tenorangesax/The-SaxplayerTM/PICTURES/FINAL/back silk.png

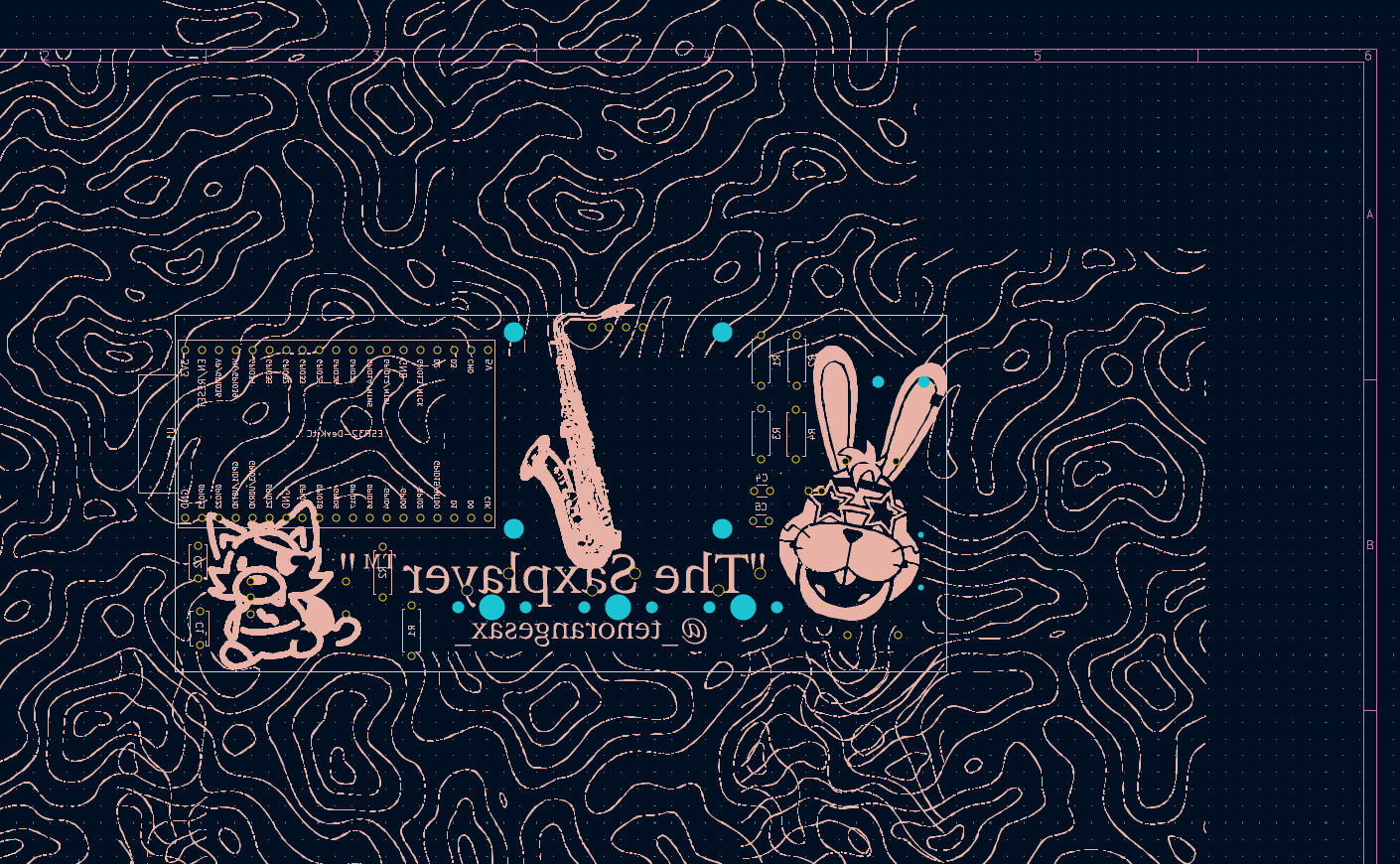
PICTURES/FINAL/back silk.png
