tenorangesax/The-SaxplayerTM/PICTURES/FINAL/Back_final.png

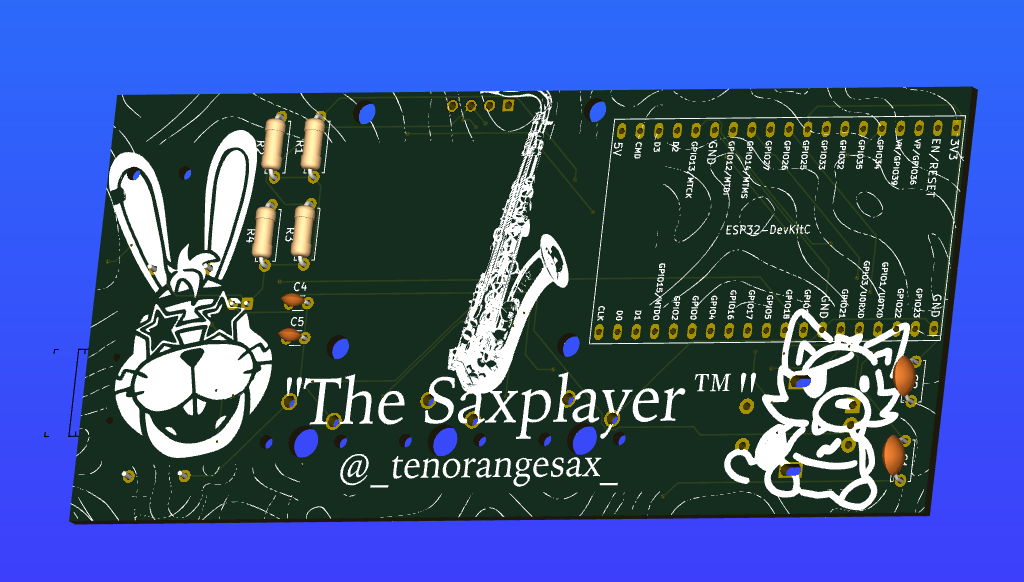
PICTURES/FINAL/Back_final.png
