tenorangesax/The-SaxplayerTM/PICTURES/FINAL/footprints.png

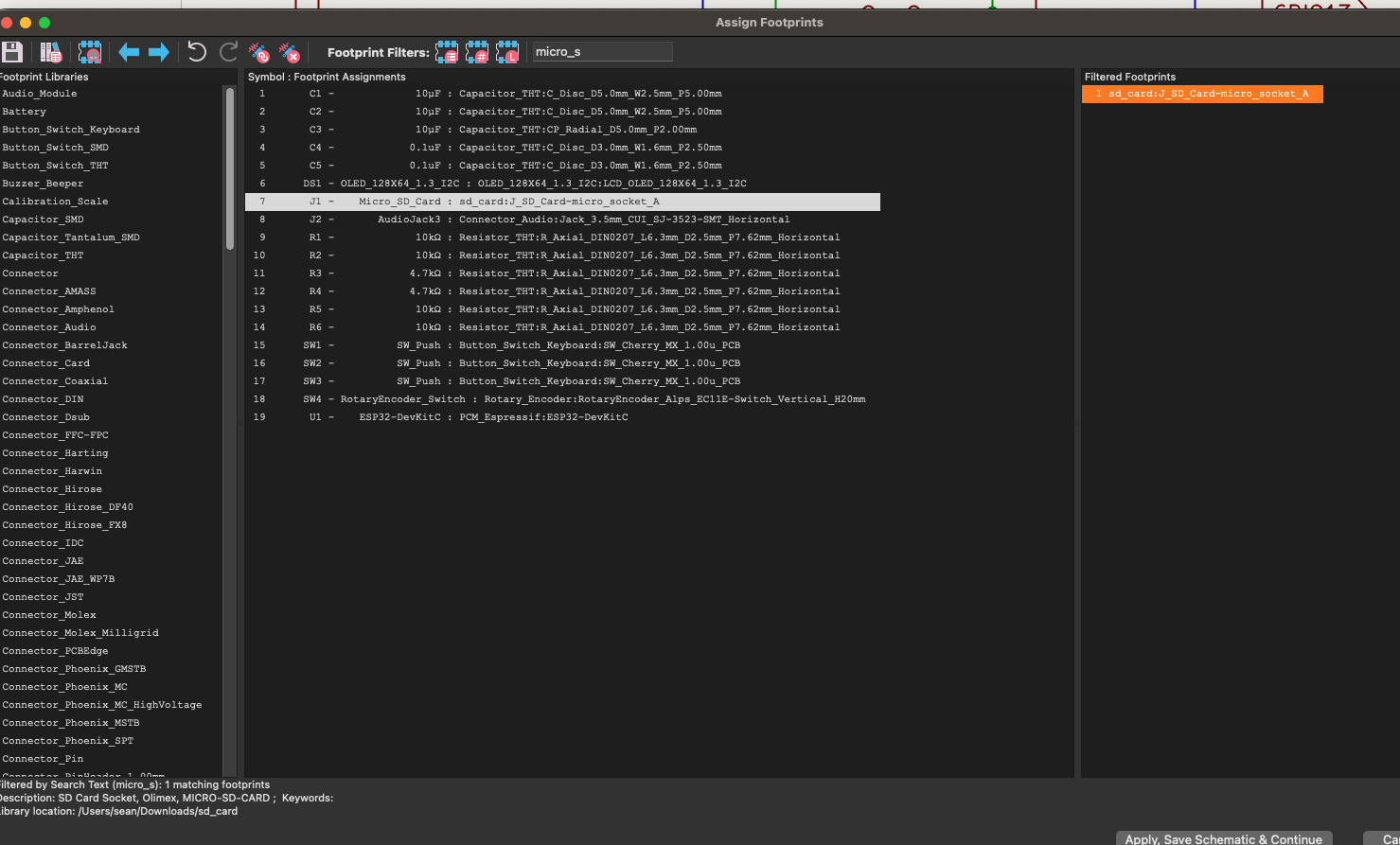
PICTURES/FINAL/footprints.png
