tenorangesax/The-SaxplayerTM/PICTURES/FINAL/front silk.png

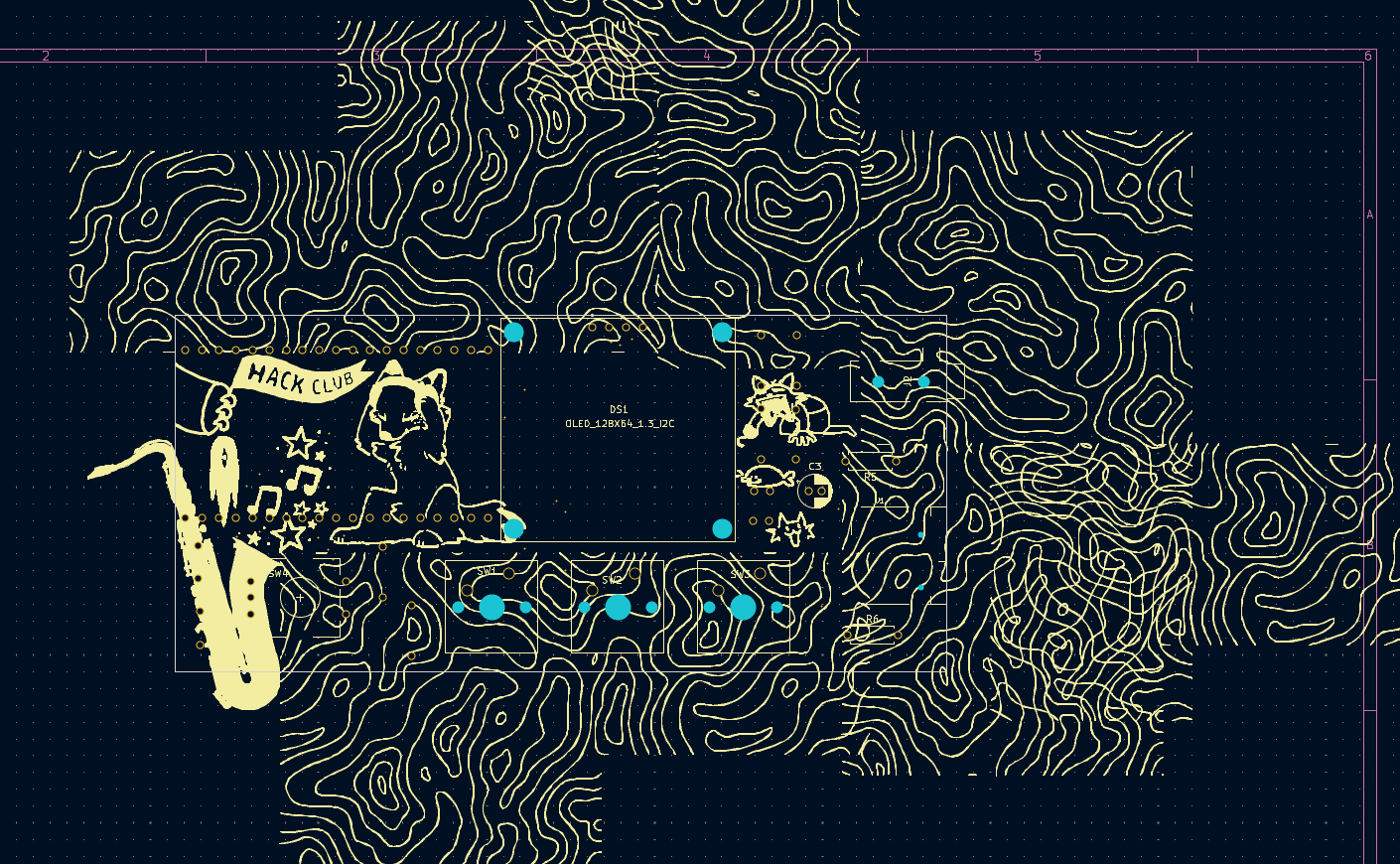
PICTURES/FINAL/front silk.png
