tenorangesax/The-SaxplayerTM/PICTURES/FINAL/IMG_7595.jpeg

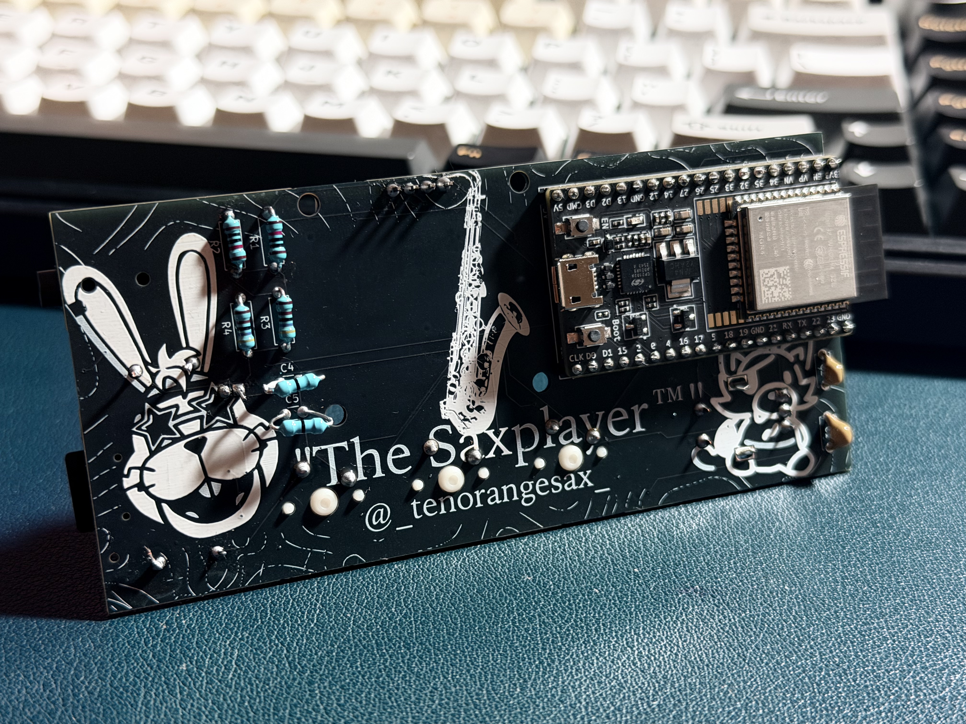
PICTURES/FINAL/IMG_7595.jpeg
