tenorangesax/The-SaxplayerTM/PICTURES/FINAL/IMG_7597.jpeg

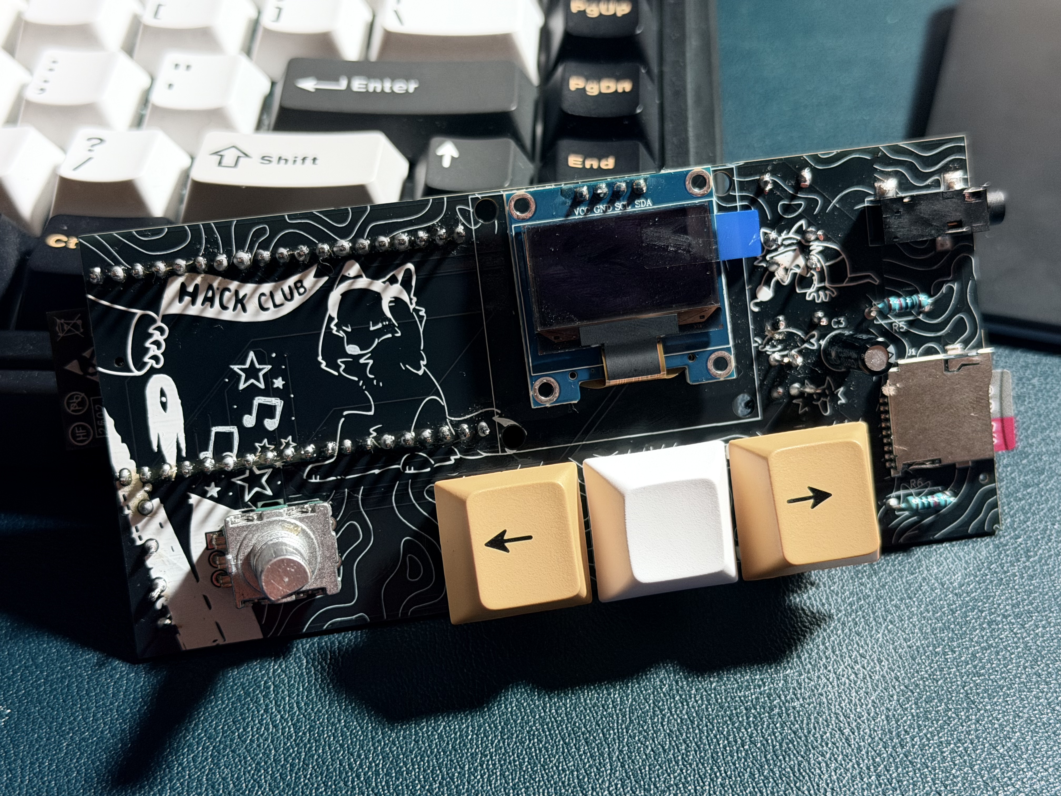
PICTURES/FINAL/IMG_7597.jpeg
