tenorangesax/The-SaxplayerTM/PICTURES/FINAL/IMG_7604.jpeg

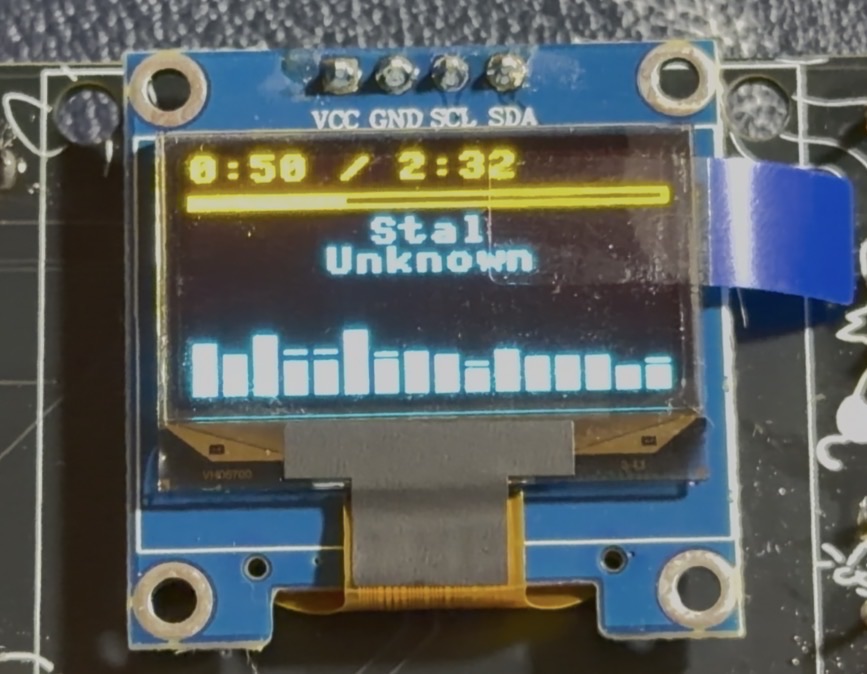
PICTURES/FINAL/IMG_7604.jpeg
