tenorangesax/The-SaxplayerTM/PICTURES/FINAL/IMG_7605.jpeg

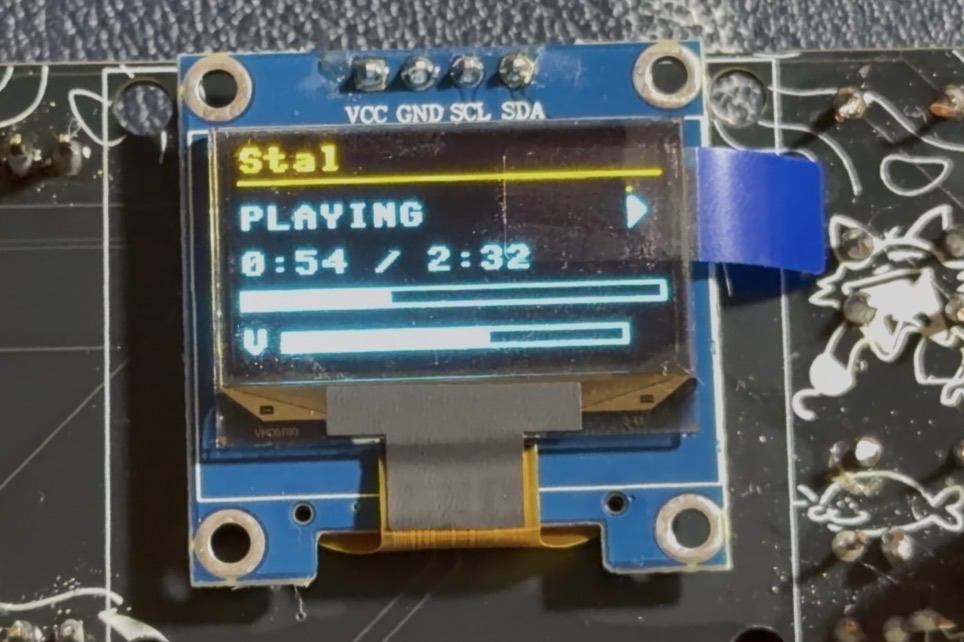
PICTURES/FINAL/IMG_7605.jpeg
