tenorangesax/The-SaxplayerTM/PICTURES/FINAL/IMG_7606.jpeg

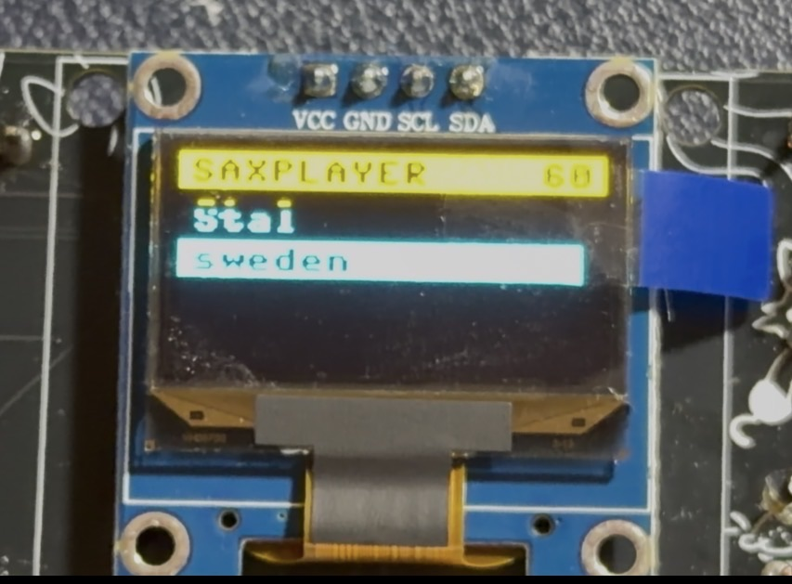
PICTURES/FINAL/IMG_7606.jpeg
