tenorangesax/The-SaxplayerTM/PICTURES/FINAL/IMG_7608.jpeg

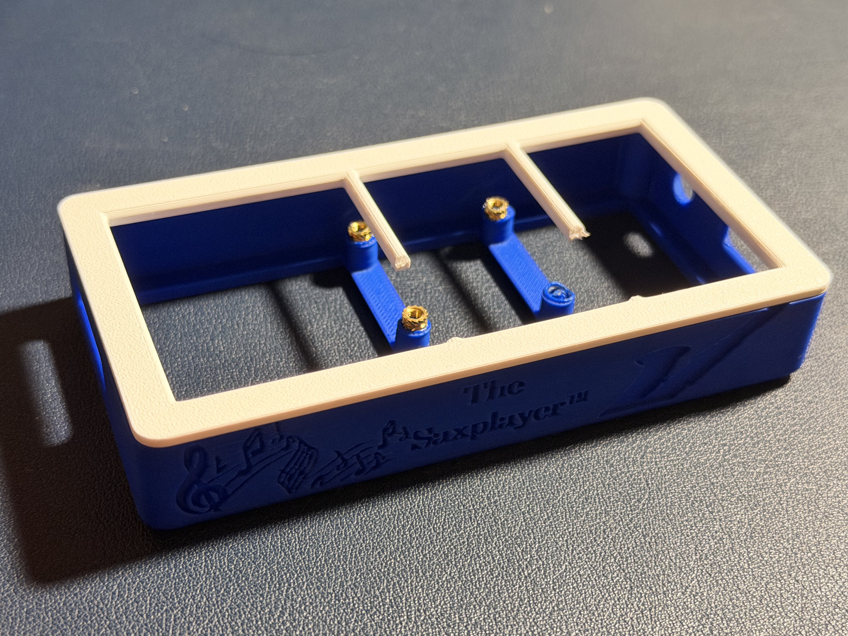
PICTURES/FINAL/IMG_7608.jpeg
