tenorangesax/The-SaxplayerTM/PICTURES/FINAL/IMG_7609.jpeg

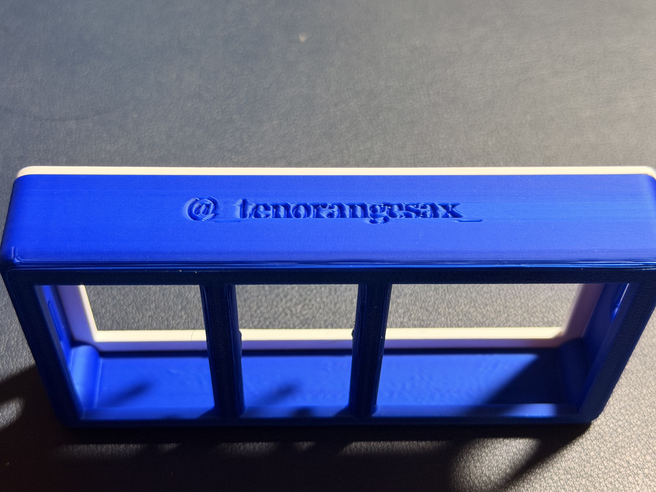
PICTURES/FINAL/IMG_7609.jpeg
