tenorangesax/The-SaxplayerTM/PICTURES/FINAL/IMG_7610.jpeg

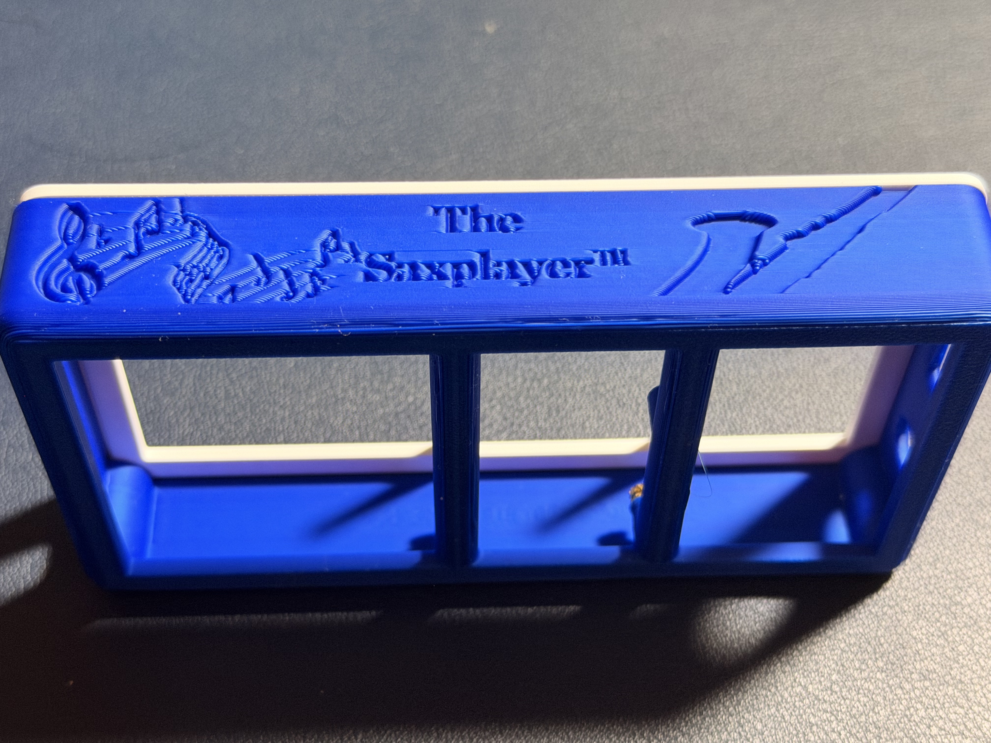
PICTURES/FINAL/IMG_7610.jpeg
