tenorangesax/The-SaxplayerTM/PICTURES/FINAL/IMG_7611.jpeg

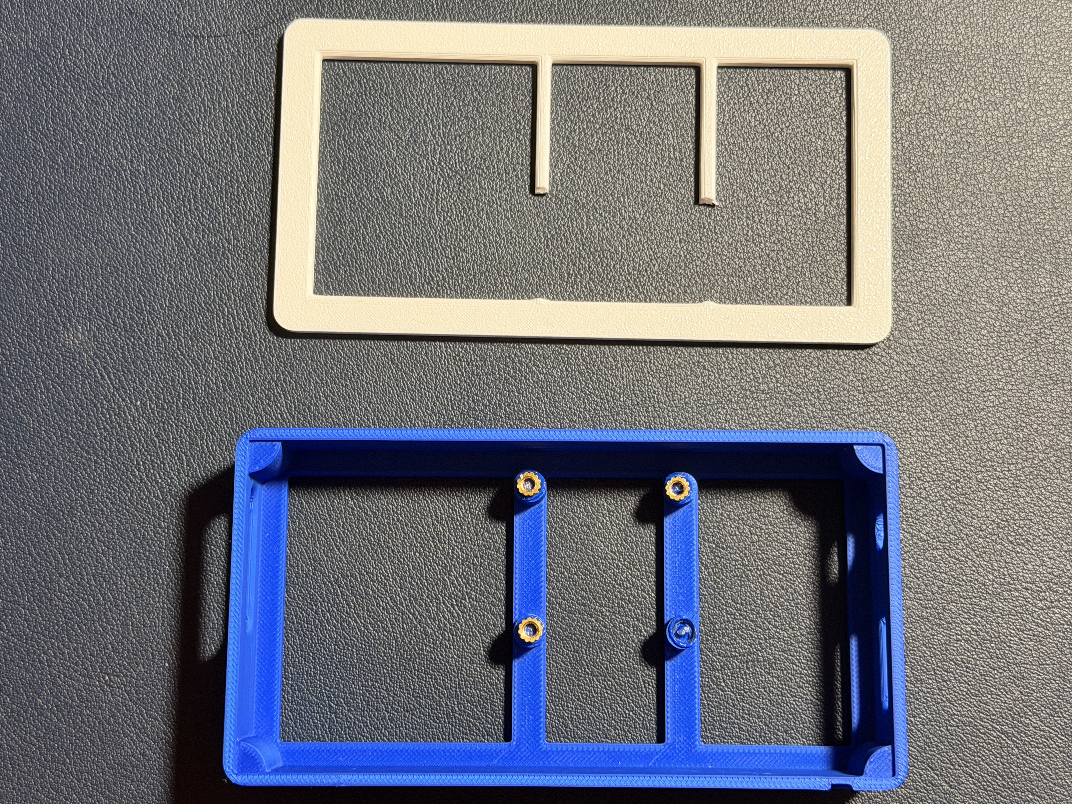
PICTURES/FINAL/IMG_7611.jpeg
