tenorangesax/The-SaxplayerTM/PICTURES/FINAL/IMG_7619.jpeg

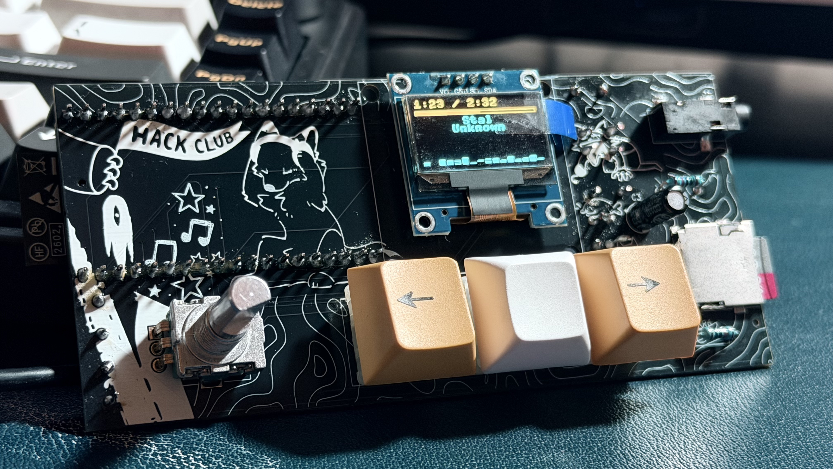
PICTURES/FINAL/IMG_7619.jpeg
