tenorangesax/The-SaxplayerTM/PICTURES/FINAL/JLCPCB BACK.png

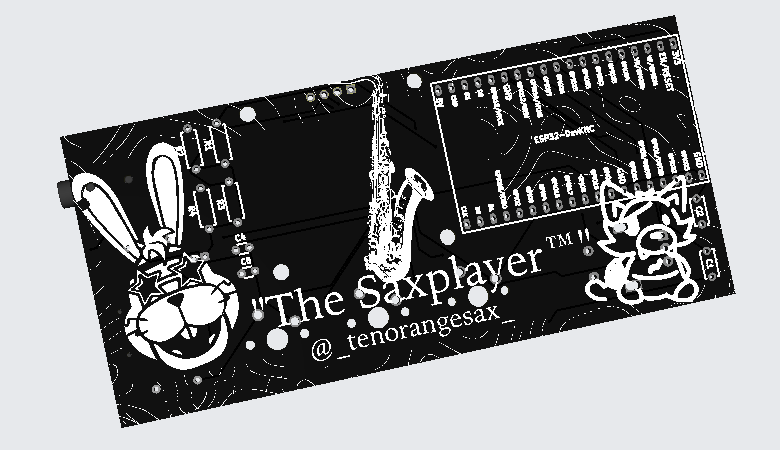
PICTURES/FINAL/JLCPCB BACK.png
