tenorangesax/The-SaxplayerTM/PICTURES/FINAL/JLCPCB FRONT.png

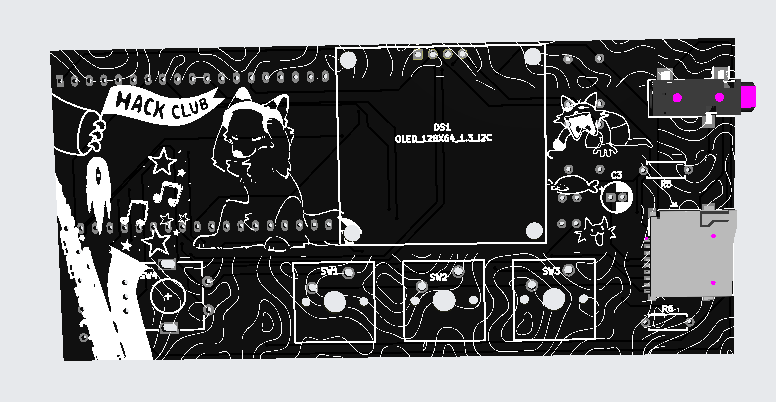
PICTURES/FINAL/JLCPCB FRONT.png
