tenorangesax/The-SaxplayerTM/PICTURES/FINAL/more footprints.png

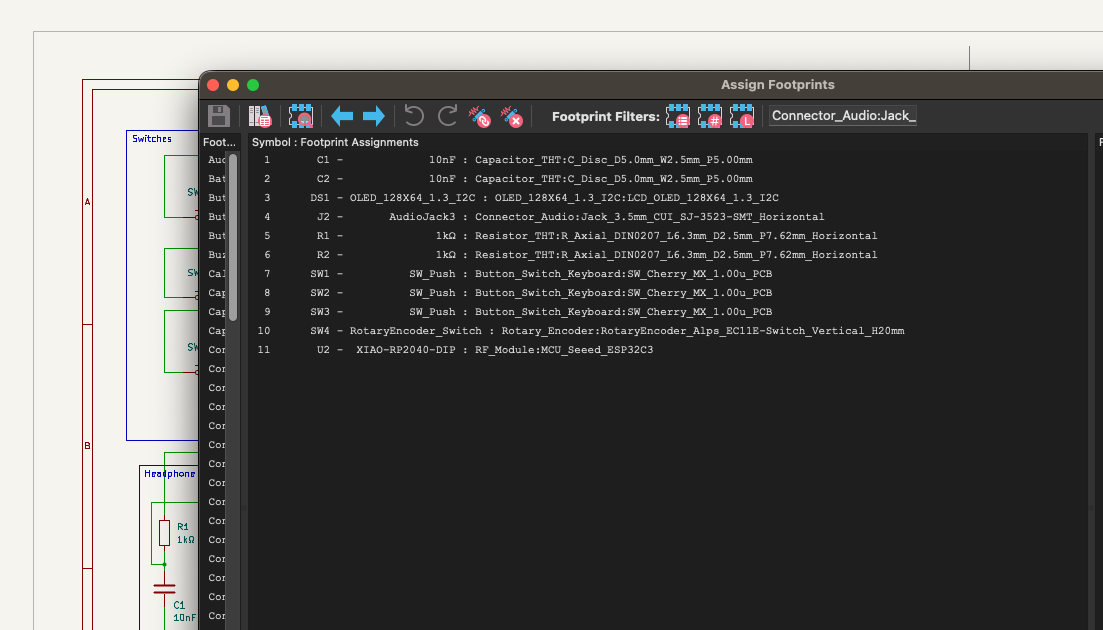
PICTURES/FINAL/more footprints.png
