tenorangesax/The-SaxplayerTM/PICTURES/FINAL/negative warnings???.png

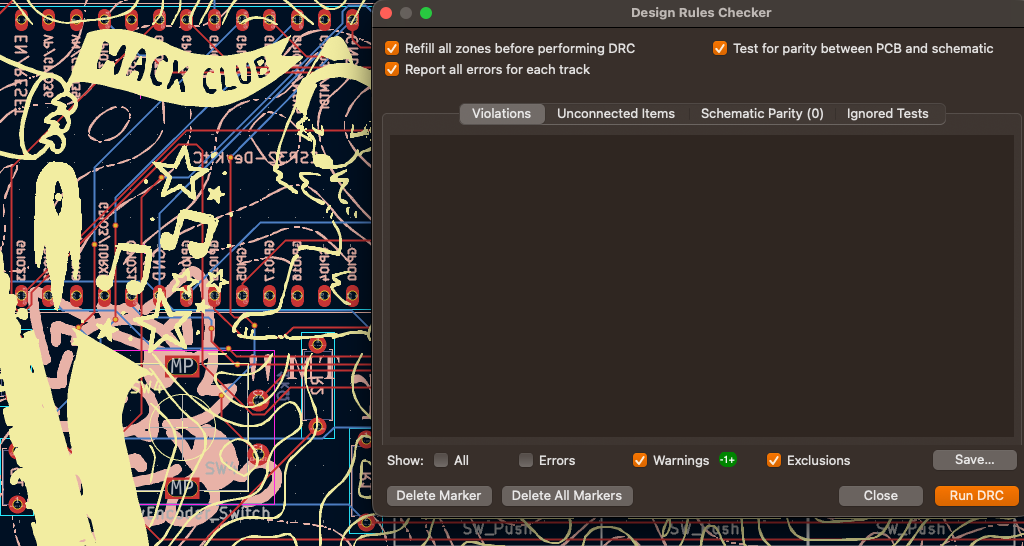
PICTURES/FINAL/negative warnings???.png
