tenorangesax/The-SaxplayerTM/PICTURES/FINAL/Saxplayer_Case_Alt_View.png

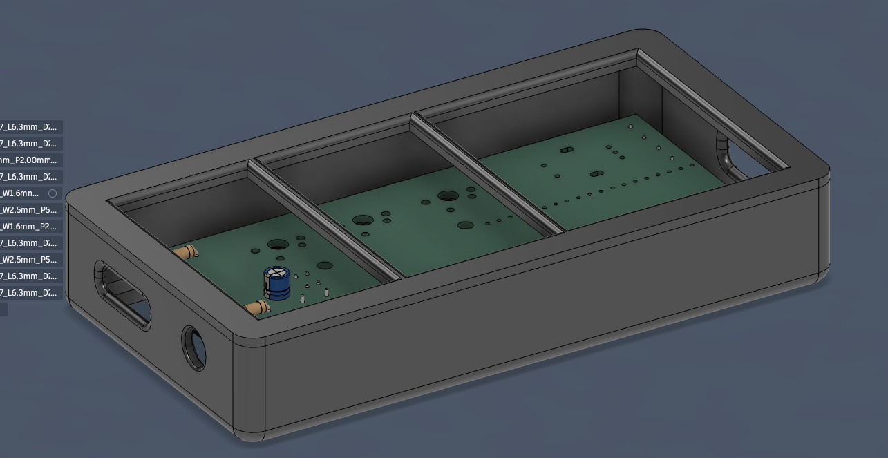
PICTURES/FINAL/Saxplayer_Case_Alt_View.png
