tenorangesax/The-SaxplayerTM/PICTURES/FINAL/Saxplayer_Case_Bottom.png

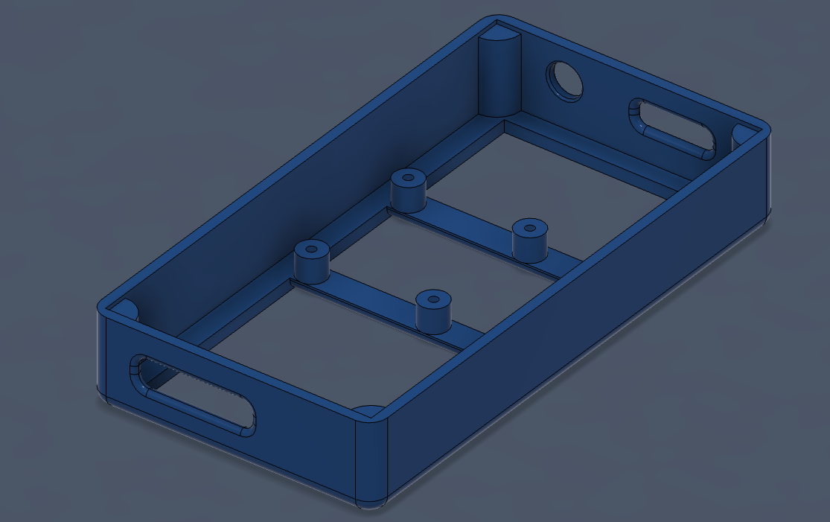
PICTURES/FINAL/Saxplayer_Case_Bottom.png
