tenorangesax/The-SaxplayerTM/PICTURES/FINAL/Saxplayer_Case_Full.png

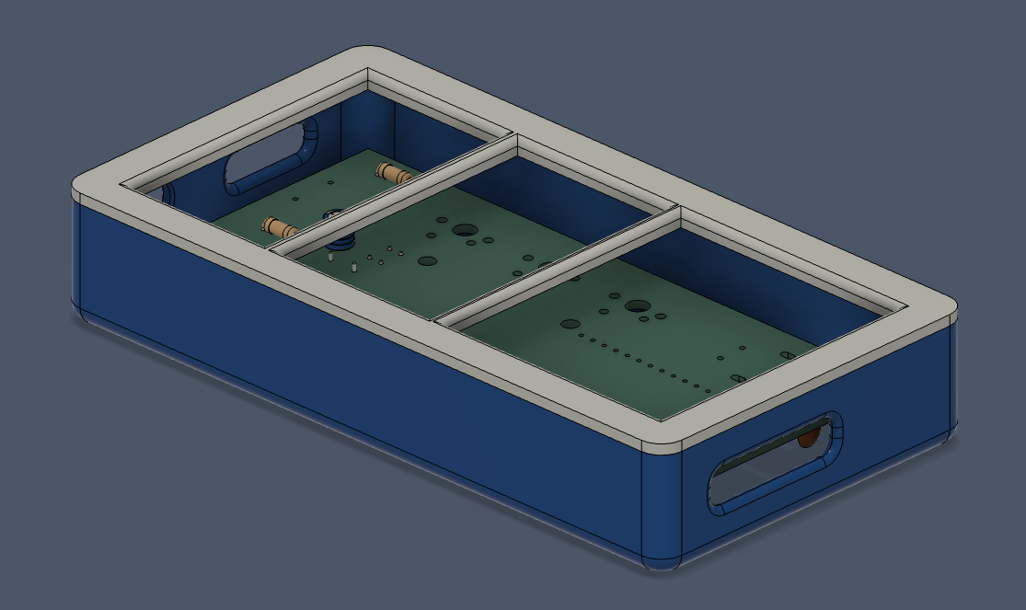
PICTURES/FINAL/Saxplayer_Case_Full.png
