tenorangesax/The-SaxplayerTM/PICTURES/FINAL/Saxplayer_Case_Top.png

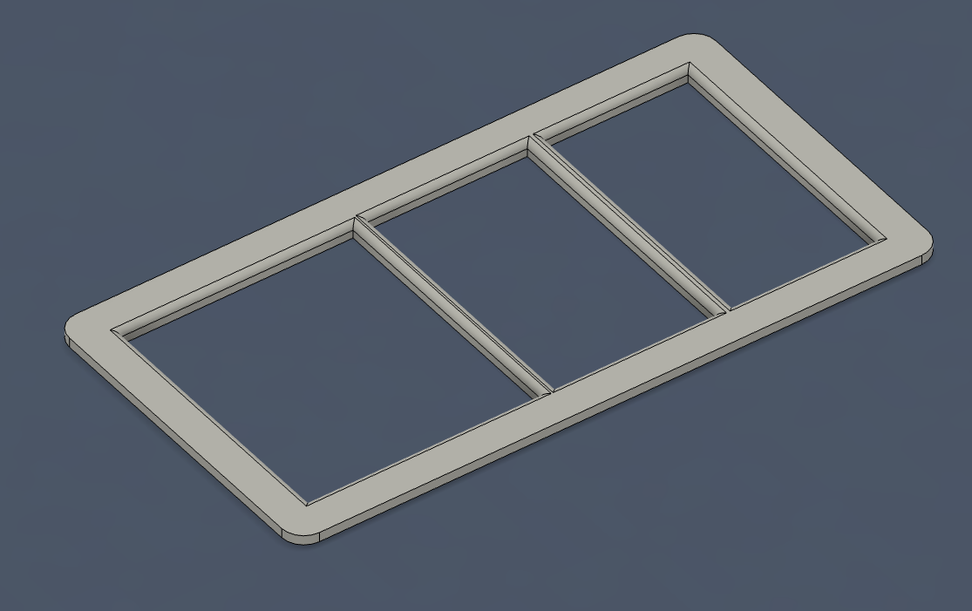
PICTURES/FINAL/Saxplayer_Case_Top.png
