tenorangesax/The-SaxplayerTM/PICTURES/FINAL/the whole mess.png

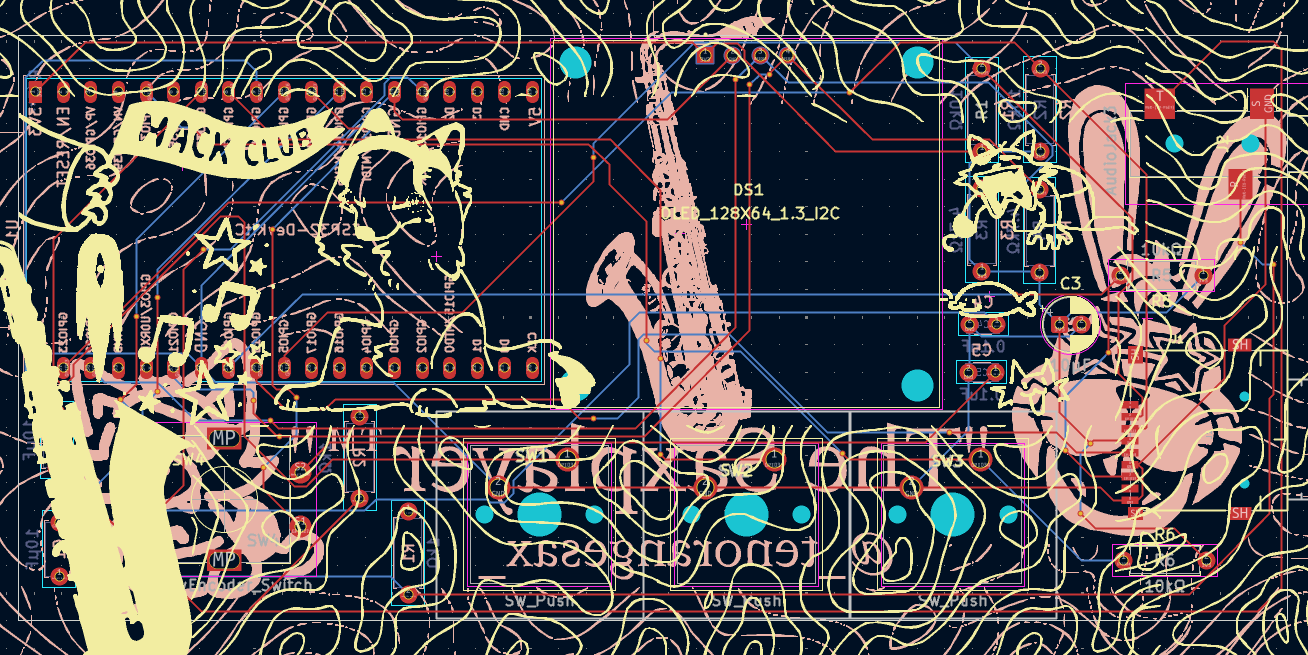
PICTURES/FINAL/the whole mess.png
