tenorangesax/The-SaxplayerTM/Extra_Materials/_ (1).jpeg

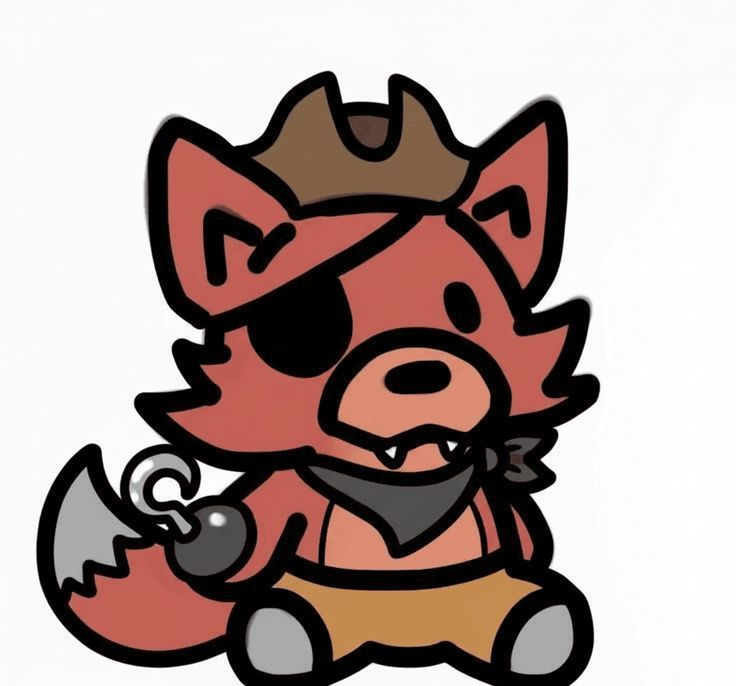
Extra_Materials/_ (1).jpeg
