tenorangesax/The-SaxplayerTM/Extra_Materials/_ (2).jpeg

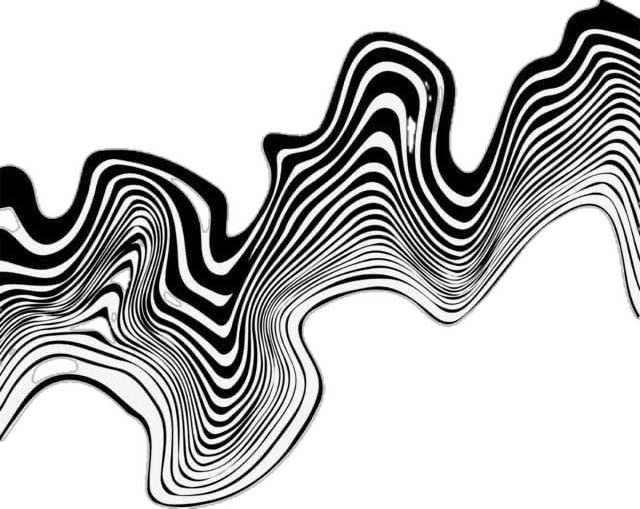
Extra_Materials/_ (2).jpeg
