tenorangesax/The-SaxplayerTM/Extra_Materials/_ (3).jpeg

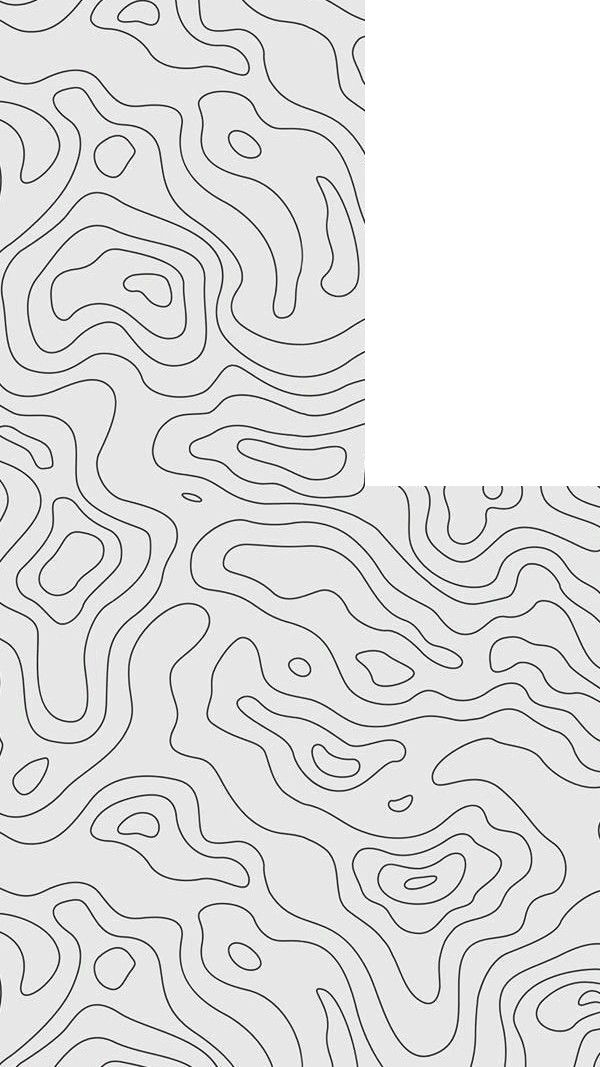
Extra_Materials/_ (3).jpeg
