tenorangesax/The-SaxplayerTM/Extra_Materials/_ (4).jpeg

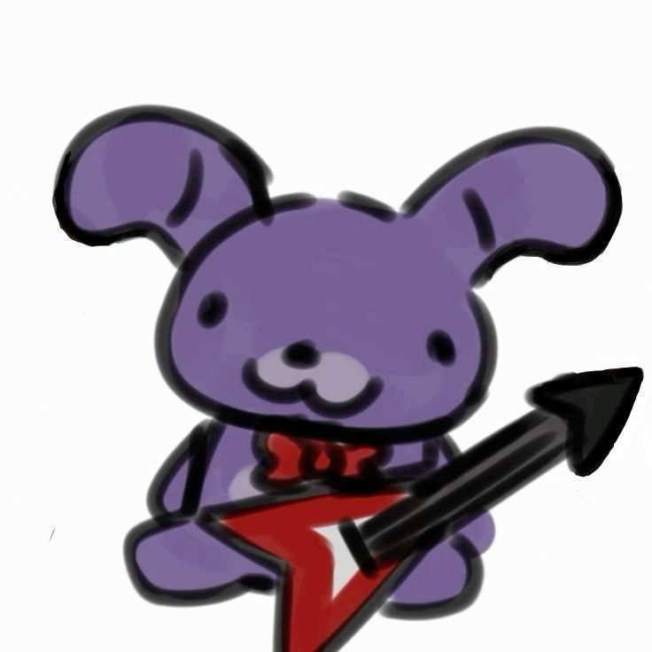
Extra_Materials/_ (4).jpeg
