tenorangesax/The-SaxplayerTM/Extra_Materials/_ (5).jpeg

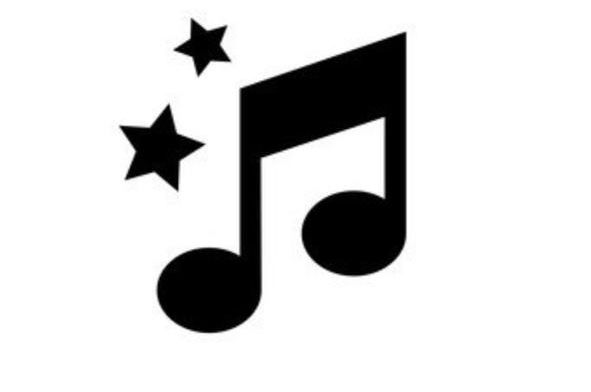
Extra_Materials/_ (5).jpeg
