tenorangesax/The-SaxplayerTM/Extra_Materials/_ (6).jpeg

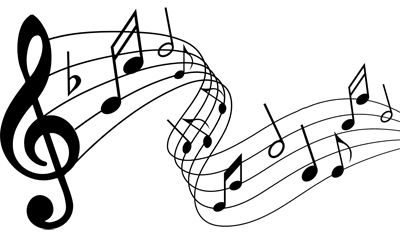
Extra_Materials/_ (6).jpeg
