tenorangesax/The-SaxplayerTM/Extra_Materials/_ (7).jpeg

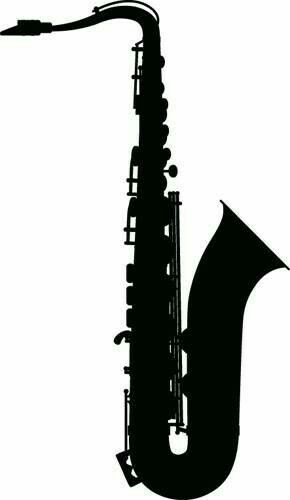
Extra_Materials/_ (7).jpeg
