tenorangesax/The-SaxplayerTM/Extra_Materials/_ (9).jpeg

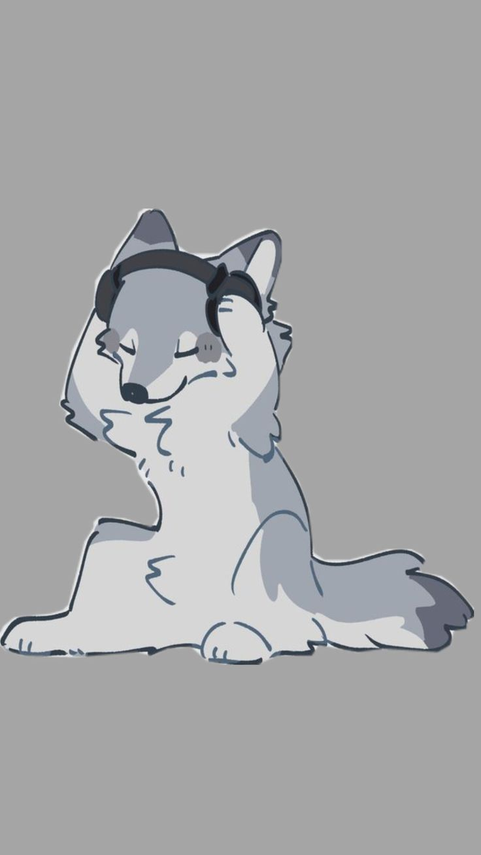
Extra_Materials/_ (9).jpeg
