tenorangesax/The-SaxplayerTM/Extra_Materials/_ (10).jpeg

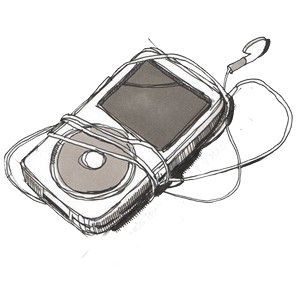
Extra_Materials/_ (10).jpeg
