tenorangesax/The-SaxplayerTM/Extra_Materials/_ (11).jpeg

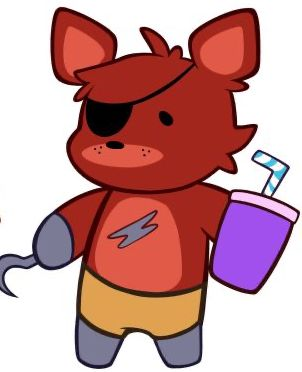
Extra_Materials/_ (11).jpeg
