tenorangesax/The-SaxplayerTM/Extra_Materials/_.jpeg

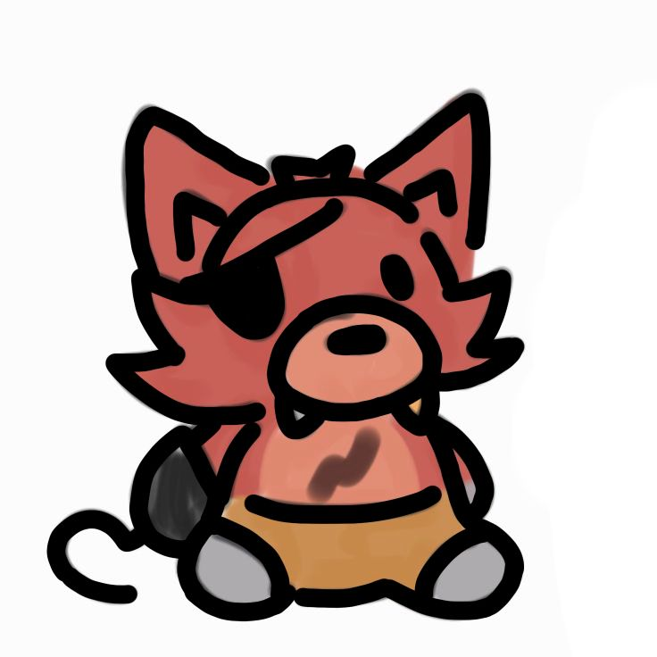
Extra_Materials/_.jpeg
