tenorangesax/The-SaxplayerTM/Extra_Materials/Download Saxophone, Sax, Woodwind_ Royalty-Free Vector Graphic.jpeg

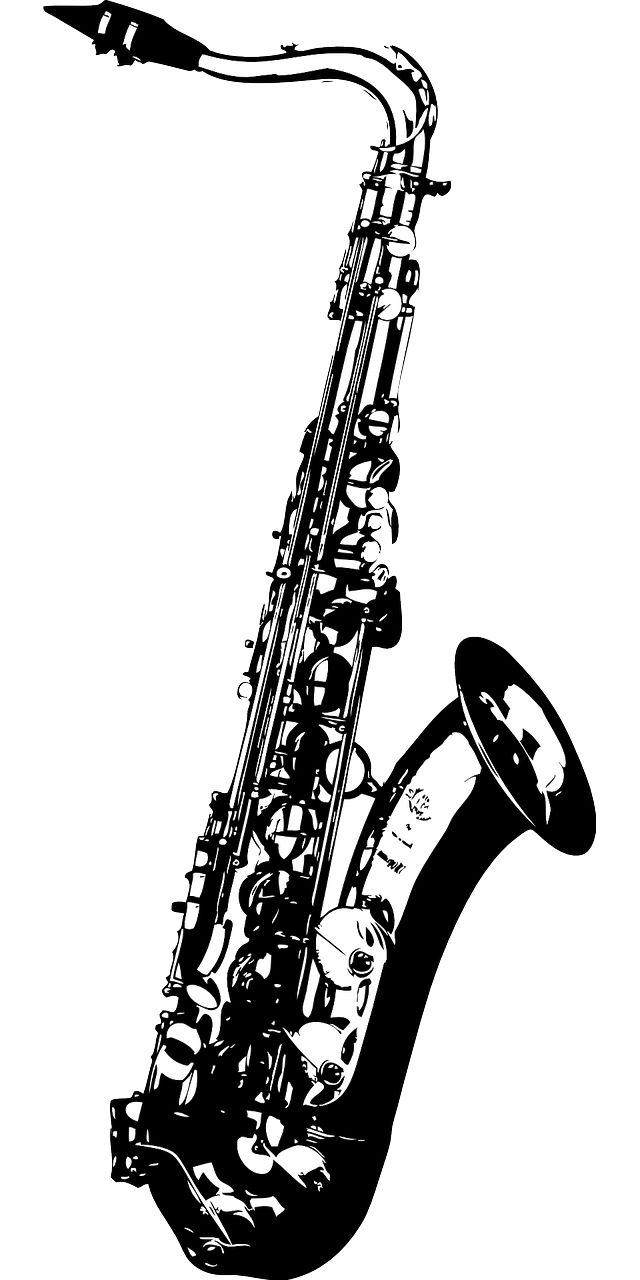
Extra_Materials/Download Saxophone, Sax, Woodwind_ Royalty-Free Vector Graphic.jpeg
