tenorangesax/The-SaxplayerTM/Extra_Materials/Follow me to get the best.jpeg

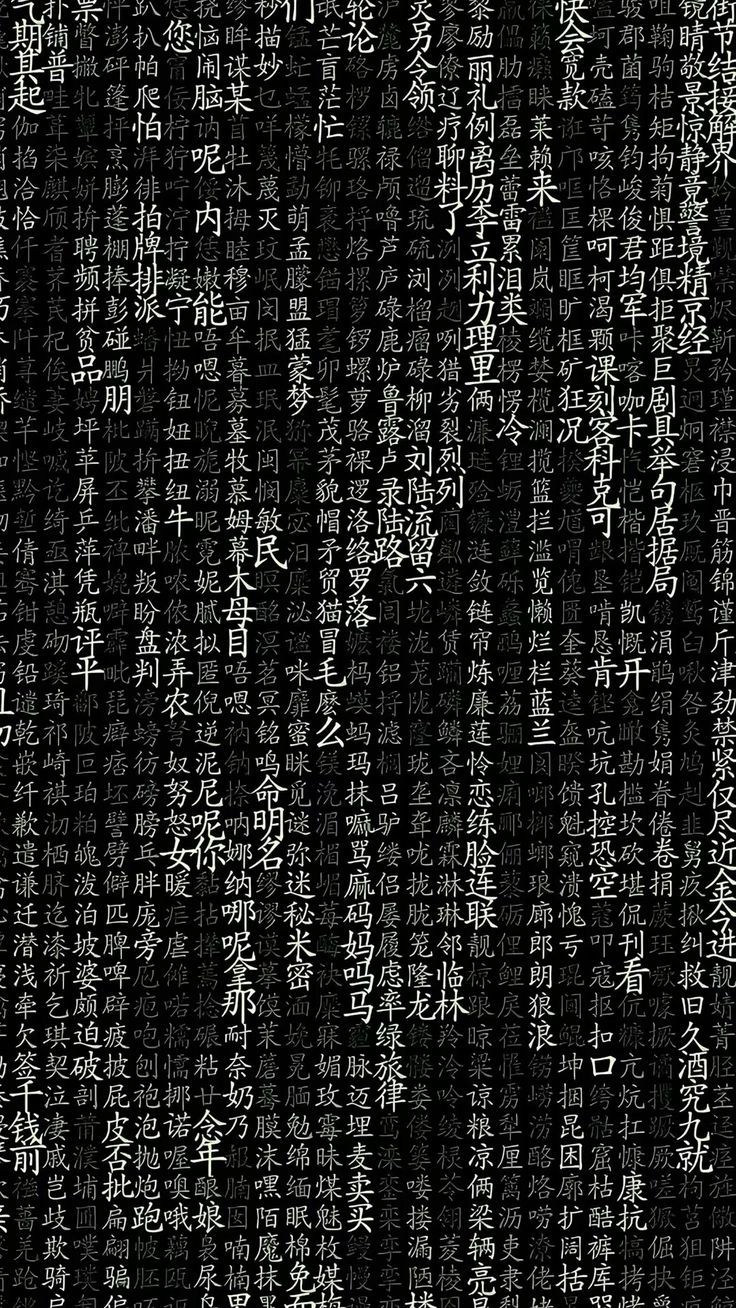
Extra_Materials/Follow me to get the best.jpeg
