tenorangesax/The-SaxplayerTM/Extra_Materials/Glamrock Bonnie Plush.jpeg

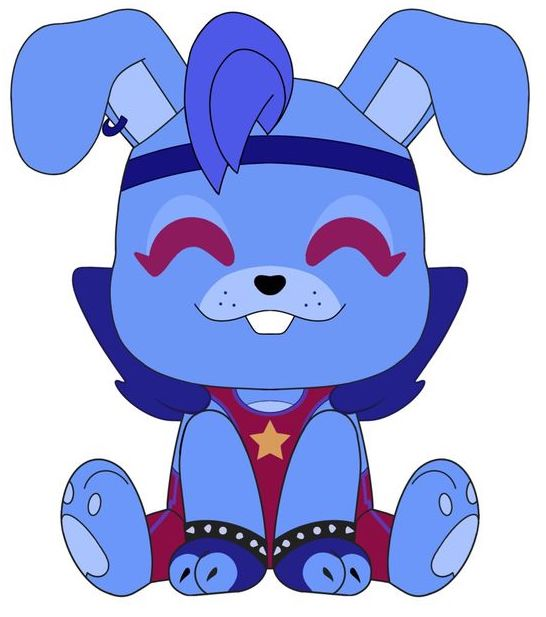
Extra_Materials/Glamrock Bonnie Plush.jpeg
