tenorangesax/The-SaxplayerTM/Extra_Materials/Silly cat _].jpeg

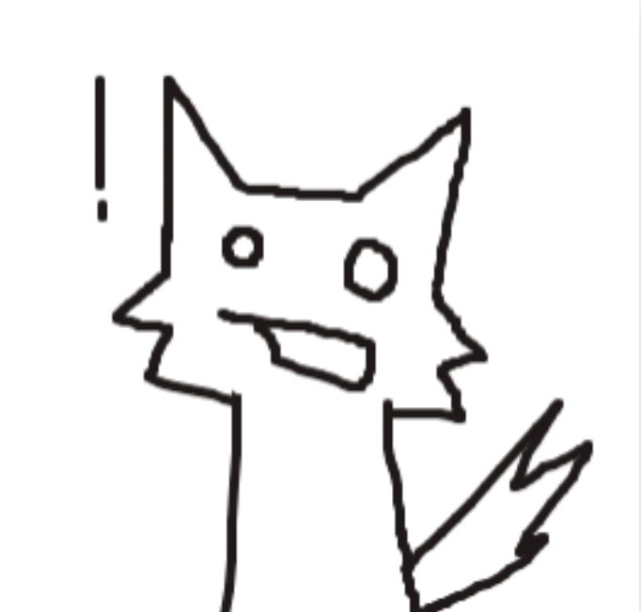
Extra_Materials/Silly cat _].jpeg
