tenorangesax/The-SaxplayerTM/Extra_Materials/theme!!.jpeg

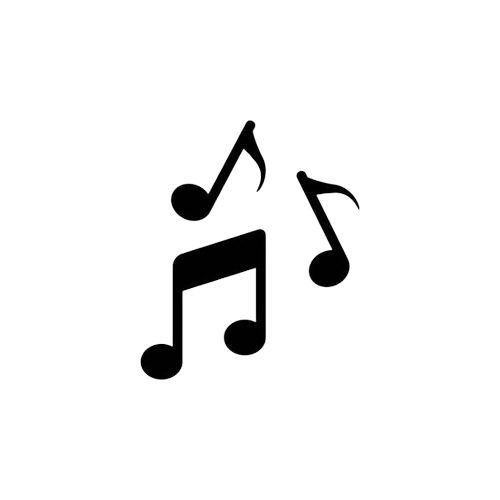
Extra_Materials/theme!!.jpeg
