tenorangesax/The-SaxplayerTM/PCB/Saxplayer.kicad_sch

## KiCad design PCB/Saxplayer.kicad_sch (2026-03-30)

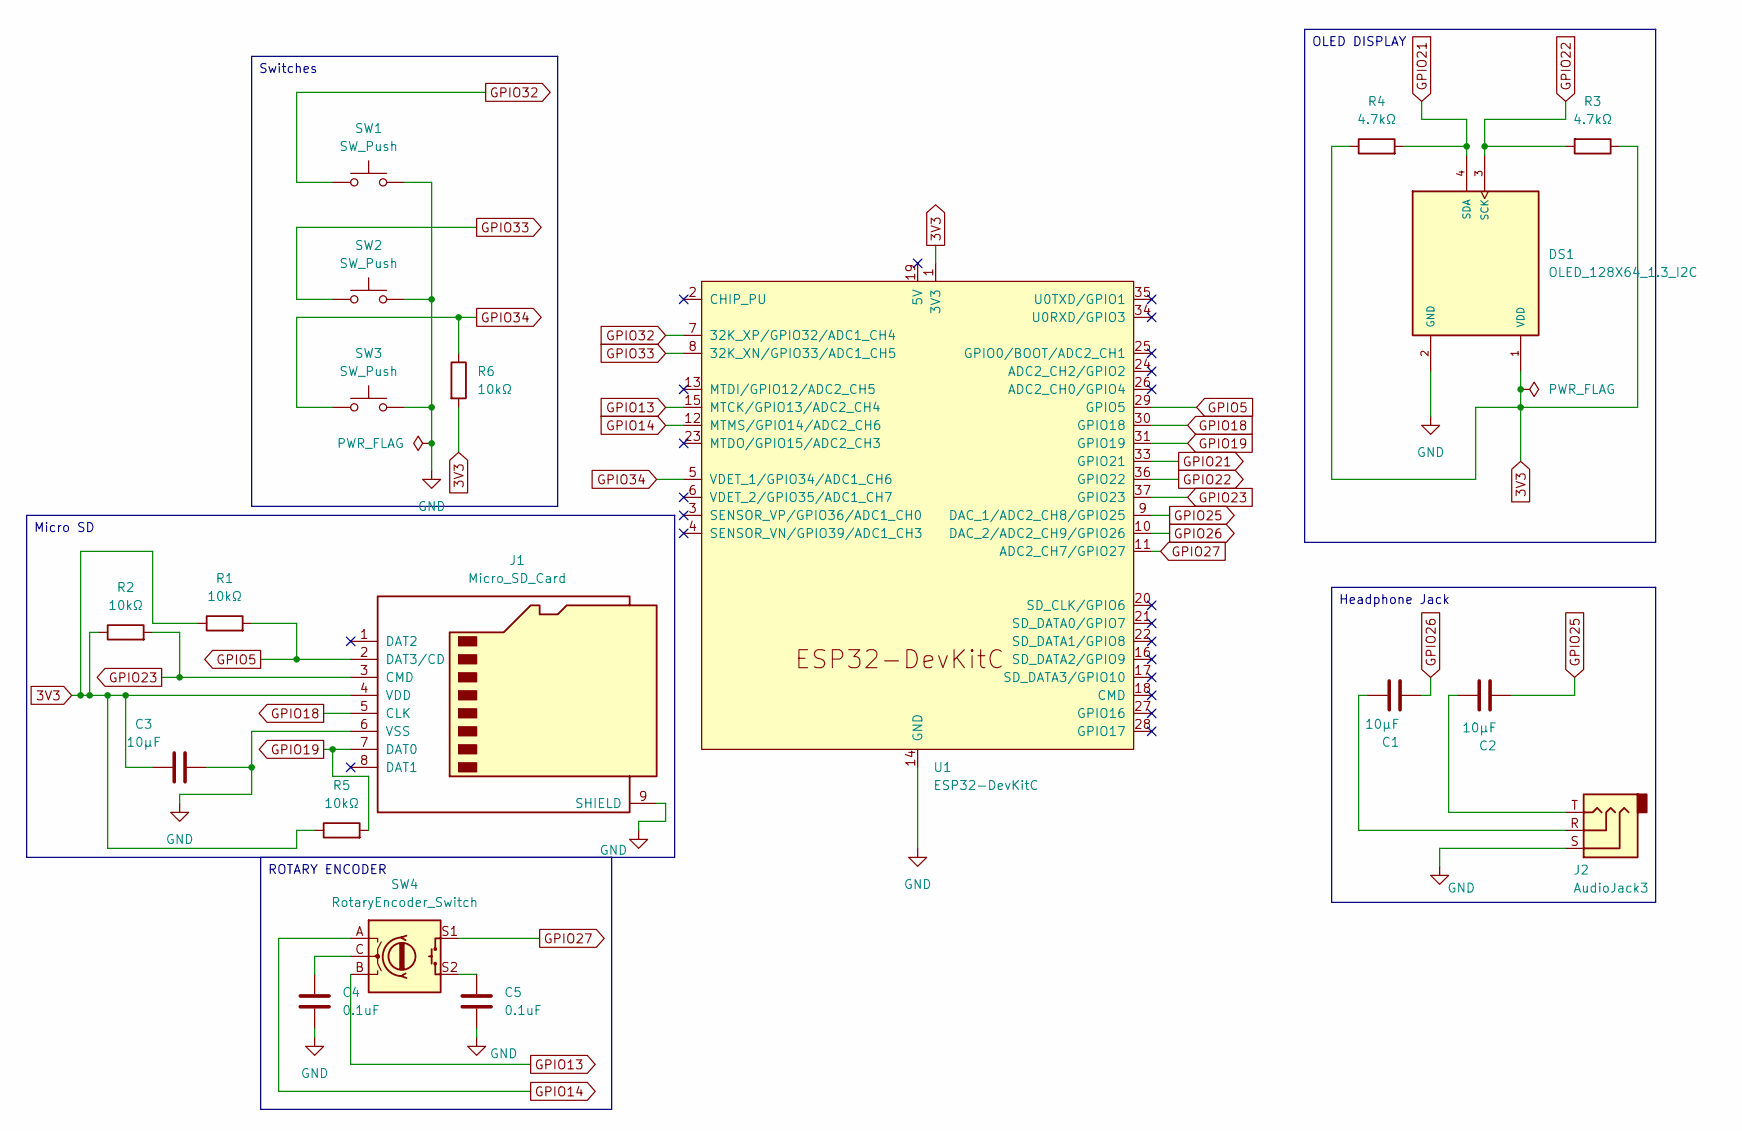
[picture p48: schematic Saxplayer.kicad_sch]

Parts:
C1, C2: 10µF; C_Disc_D5.0mm_W2.5mm_P5.00mm
C3: 10µF; CP_Radial_D5.0mm_P2.00mm
C4, C5: 0.1uF; C_Disc_D3.0mm_W1.6mm_P2.50mm
DS1: OLED_128X64_1.3_I2C; LCD_OLED_128X64_1.3_I2C; PARTREV NA
J1: Micro_SD_Card; J_SD_Card-micro_socket_A
J2: AudioJack3; Jack_3.5mm_CUI_SJ-3523-SMT_Horizontal
R1, R2, R5, R6: 10kΩ; R_Axial_DIN0207_L6.3mm_D2.5mm_P7.62mm_Horizontal
R3, R4: 4.7kΩ; R_Axial_DIN0207_L6.3mm_D2.5mm_P7.62mm_Horizontal
SW1, SW2, SW3: SW_Push; SW_Cherry_MX_1.00u_PCB
SW4: RotaryEncoder_Switch; RotaryEncoder_Alps_EC11E-Switch_Vertical_H20mm
U1: ESP32-DevKitC

Connections:
3V3: C3.1, DS1.1 (VDD), J1.4 (VDD), R1.1, R2.1, R3.1, R4.1, R5.1, R6.2, U1.1 (3V3)
GND: C3.2, C4.2, C5.2, DS1.2 (GND), J1.6 (VSS), J1.9 (SHIELD), J2.S, SW1.2, SW2.2, SW3.2, U1.14 (GND), U1.32 (GND), U1.38 (GND)
GPIO5: J1.2 (DAT3/CD), R1.2, U1.29 (GPIO5)
GPIO13: SW4.B, U1.15 (MTCK/GPIO13/ADC2_CH4)
GPIO14: SW4.A, U1.12 (MTMS/GPIO14/ADC2_CH6)
GPIO18: J1.5 (CLK), U1.30 (GPIO18)
GPIO19: J1.7 (DAT0), R5.2, U1.31 (GPIO19)
GPIO21: DS1.4 (SDA), R4.2, U1.33 (GPIO21)
GPIO22: DS1.3 (SCK), R3.2, U1.36 (GPIO22)
GPIO23: J1.3 (CMD), R2.2, U1.37 (GPIO23)
GPIO25: C2.2, U1.9 (DAC_1/ADC2_CH8/GPIO25)
GPIO26: C1.2, U1.10 (DAC_2/ADC2_CH9/GPIO26)
GPIO27: SW4.S1, U1.11 (ADC2_CH7/GPIO27)
GPIO32: SW1.1, U1.7 (32K_XP/GPIO32/ADC1_CH4)
GPIO33: SW2.1, U1.8 (32K_XN/GPIO33/ADC1_CH5)
GPIO34: R6.1, SW3.1, U1.5 (VDET_1/GPIO34/ADC1_CH6)
unnamed: C1.1, J2.R
unnamed: C2.1, J2.T
unnamed: C4.1, SW4.C
unnamed: C5.1, SW4.S2

Notes on the sheet:
Micro SD
OLED DISPLAY
Switches
Headphone Jack
ROTARY ENCODER
